pnadig1-asu/Redline-Rotary/cad/rewankelrotaryengine-2/eccentric shaft.SLDPRT

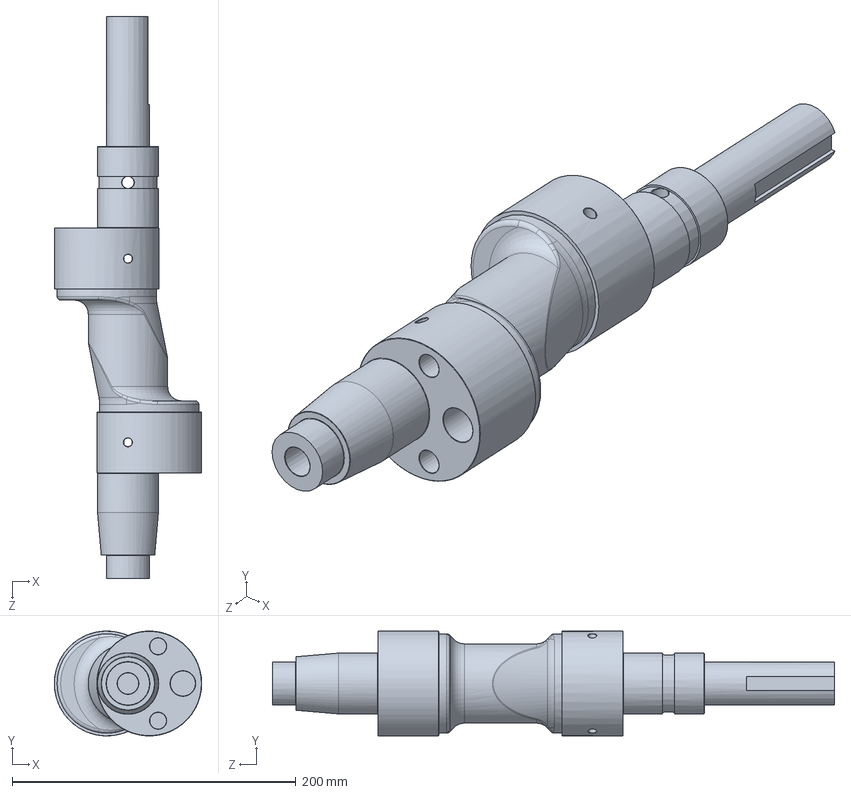
[picture p61: CAD file, 2026-03-24]
cad/rewankelrotaryengine-2/eccentric shaft.SLDPRT
104.0 x 73.9 x 396.4 mm
