pnadig1-asu/Redline-Rotary/cad/rewankelrotaryengine-2/Center electrode.SLDPRT

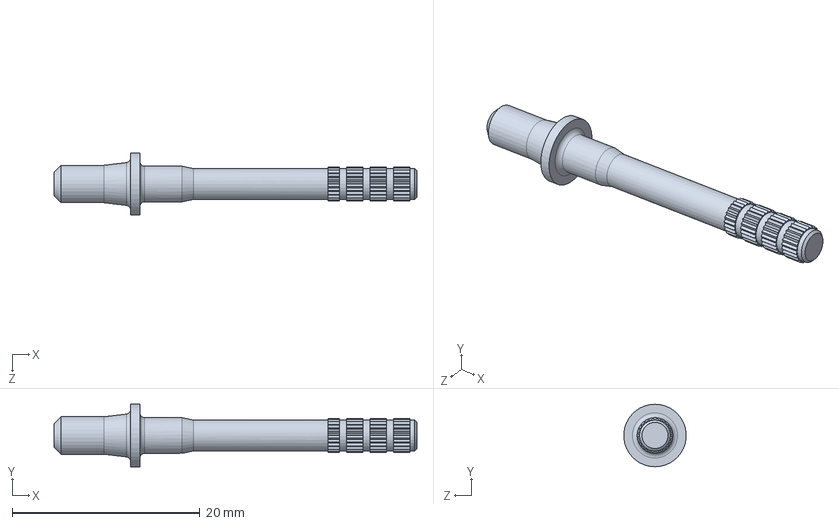
[picture p62: CAD file, 2026-03-24]
cad/rewankelrotaryengine-2/Center electrode.SLDPRT
38.7 x 6.66 x 6.64 mm
