pnadig1-asu/Redline-Rotary/cad/rewankelrotaryengine-2/lock but.SLDPRT

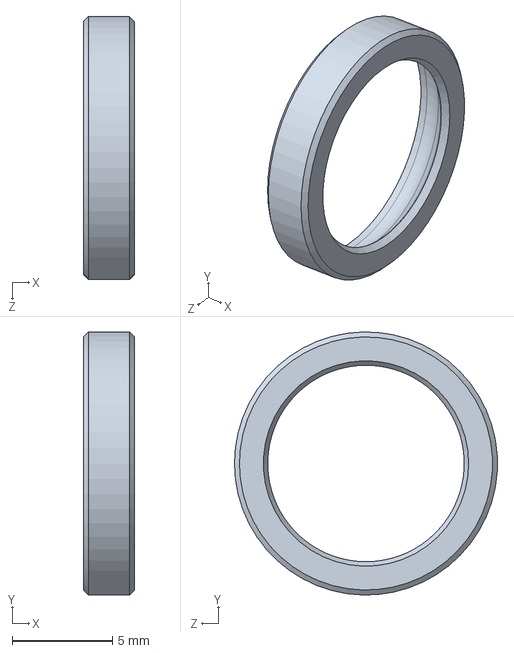
[picture p63: CAD file, 2026-03-24]
cad/rewankelrotaryengine-2/lock but.SLDPRT
2.55 x 13.1 x 13.1 mm
