pnadig1-asu/Redline-Rotary/cad/rewankelrotaryengine-2/hexagon.SLDPRT

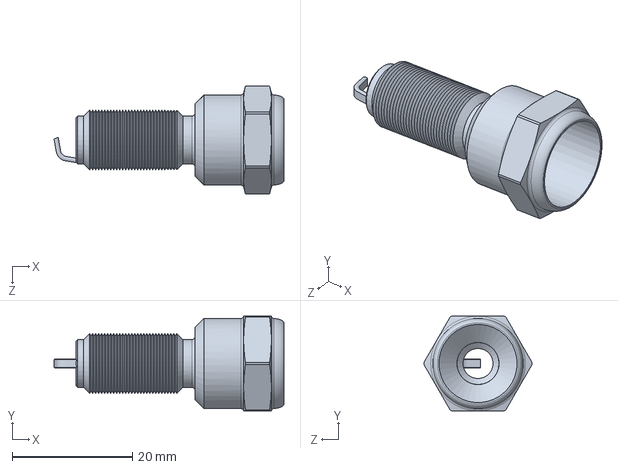
[picture p64: CAD file, 2026-03-24]
cad/rewankelrotaryengine-2/hexagon.SLDPRT
38.2 x 15.8 x 18.0 mm
