pnadig1-asu/Redline-Rotary/cad/rewankelrotaryengine-2/Inner gasket.SLDPRT

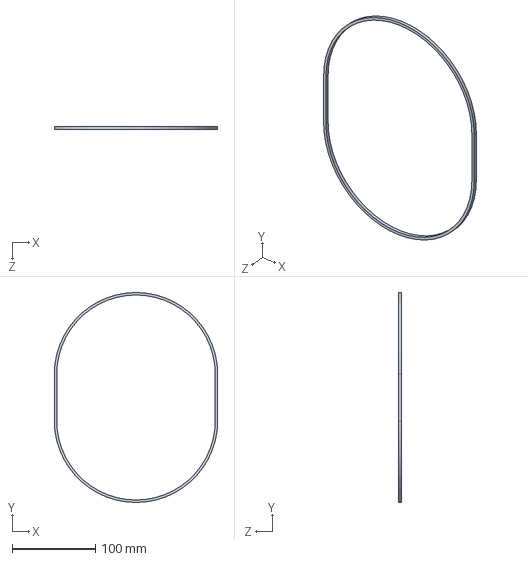
[picture p65: CAD file, 2026-03-24]
cad/rewankelrotaryengine-2/Inner gasket.SLDPRT
196.0 x 251.8 x 3.75 mm
