pnadig1-asu/Redline-Rotary/cad/rewankelrotaryengine-2/outer gasket.SLDPRT

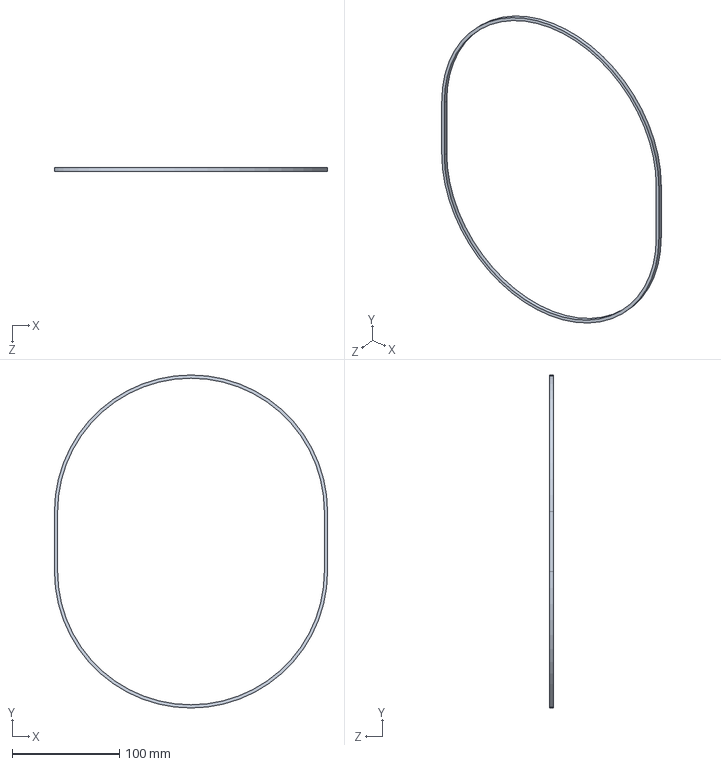
[picture p66: CAD file, 2026-03-24]
cad/rewankelrotaryengine-2/outer gasket.SLDPRT
254.4 x 310.1 x 3.75 mm
