pnadig1-asu/Redline-Rotary/cad/rewankelrotaryengine-2/electrode.SLDPRT

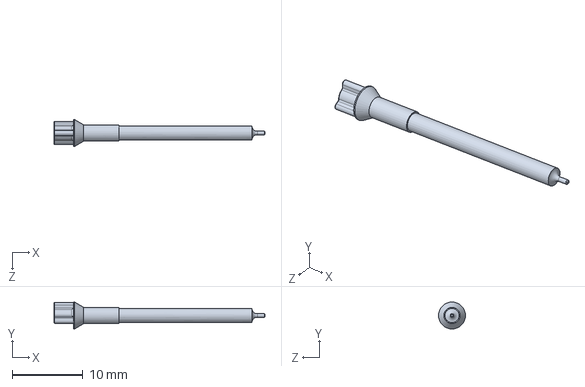
[picture p67: CAD file, 2026-03-24]
cad/rewankelrotaryengine-2/electrode.SLDPRT
29.8 x 3.80 x 3.80 mm
