pnadig1-asu/Redline-Rotary/cad/rewankelrotaryengine-2/Center block.SLDPRT

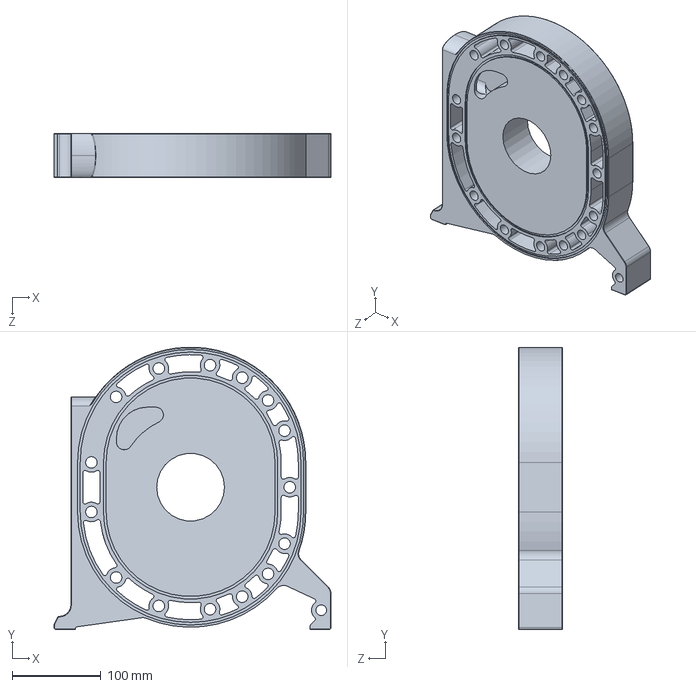
[picture p68: CAD file, 2026-03-24]
cad/rewankelrotaryengine-2/Center block.SLDPRT
311.7 x 317.8 x 50.0 mm
