pnadig1-asu/Redline-Rotary/cad/rewankelrotaryengine-2/wankel assembly.SLDASM

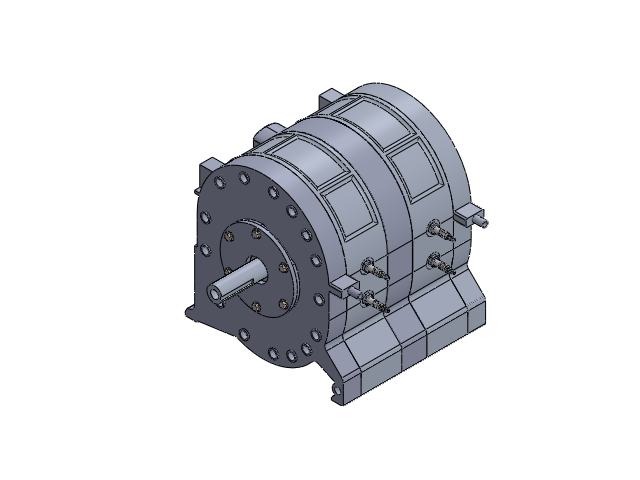
[picture p70: CAD file, 2026-03-24]
cad/rewankelrotaryengine-2/wankel assembly.SLDASM
Center block
Inner gasket x 4
outer gasket x 4
rotor housing x 2
eccentric shaft
Rotor head x 2
gearforrotor x 2
sideseal x 4
sideseal2 x 4
sideseal3 x 12
apex seals x 6
springs for apex seals x 6
apex seal washer x 12
socket head cap screw_iso x 18
frontrear gear shaft x 2
spur gear_iso x 2
Front plate
rear plate
hexagon x 4
insulator x 4
Center electrode x 4
Terminal nut x 4
electrode x 4
gasket x 4
lock but x 4
electrodes connector x 4
hex bolt gradec_iso x 12
plain washer 10673 type snl_iso x 12
